phlegeton/epic/docs/images/pbalt.jpg

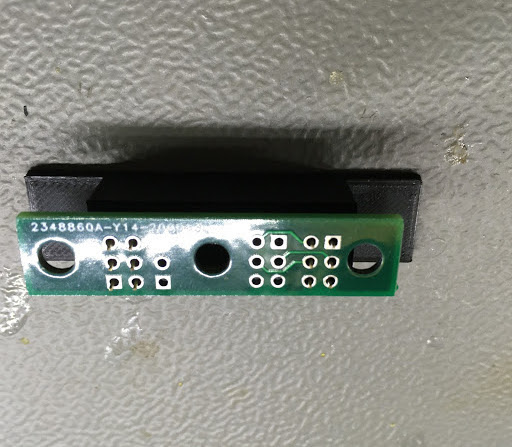
docs/images/pbalt.jpg
