phlegeton/epic/docs/images/pichatas.jpg

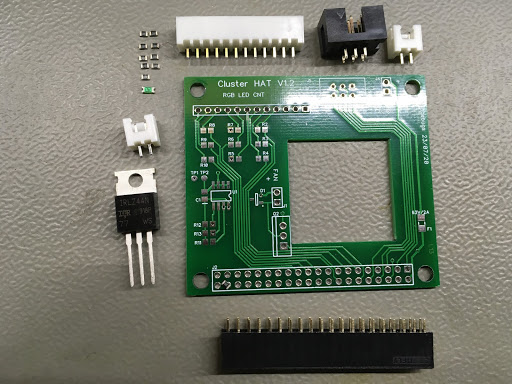
docs/images/pichatas.jpg
