phlegeton/epic/docs/images/pichfix.jpg

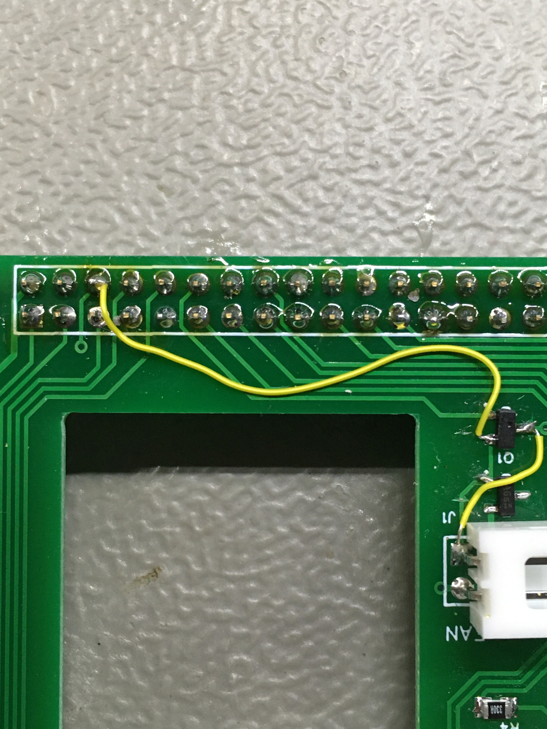
docs/images/pichfix.jpg
