phlegeton/epic/docs/images/pitp2.jpg

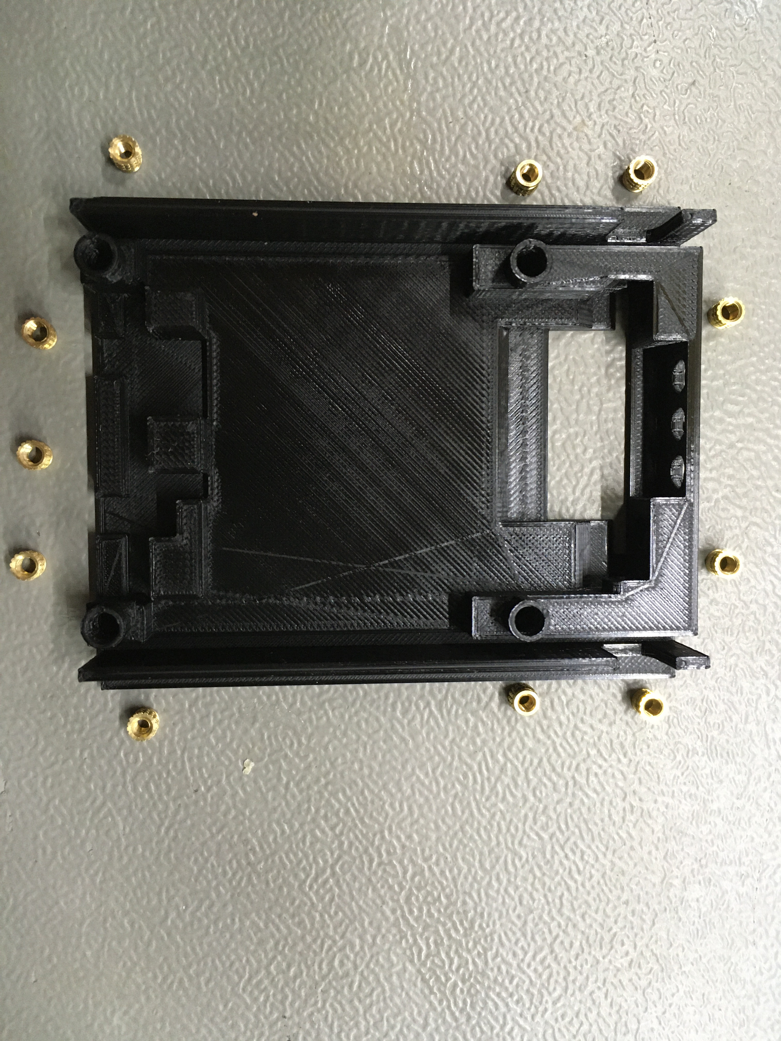
docs/images/pitp2.jpg
