phlegeton/epic/docs/images/rgb_cbl_orientation.jpg

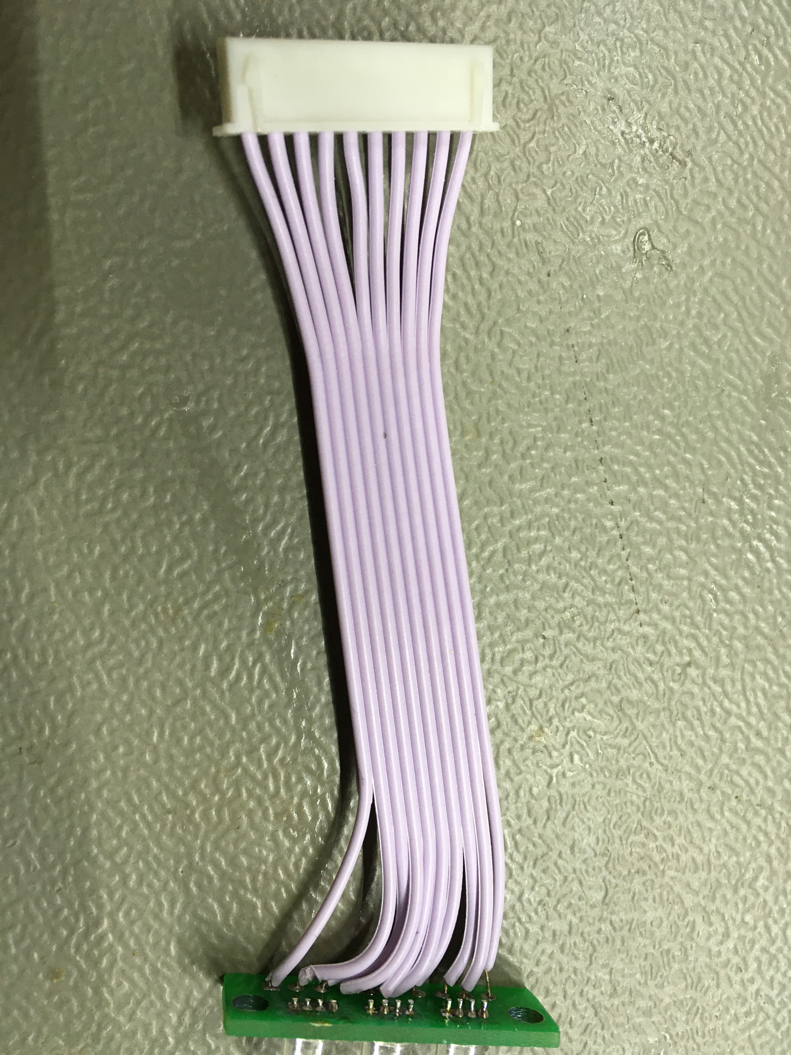
docs/images/rgb_cbl_orientation.jpg
