phlegeton/epic/docs/images/srgblwht.jpg

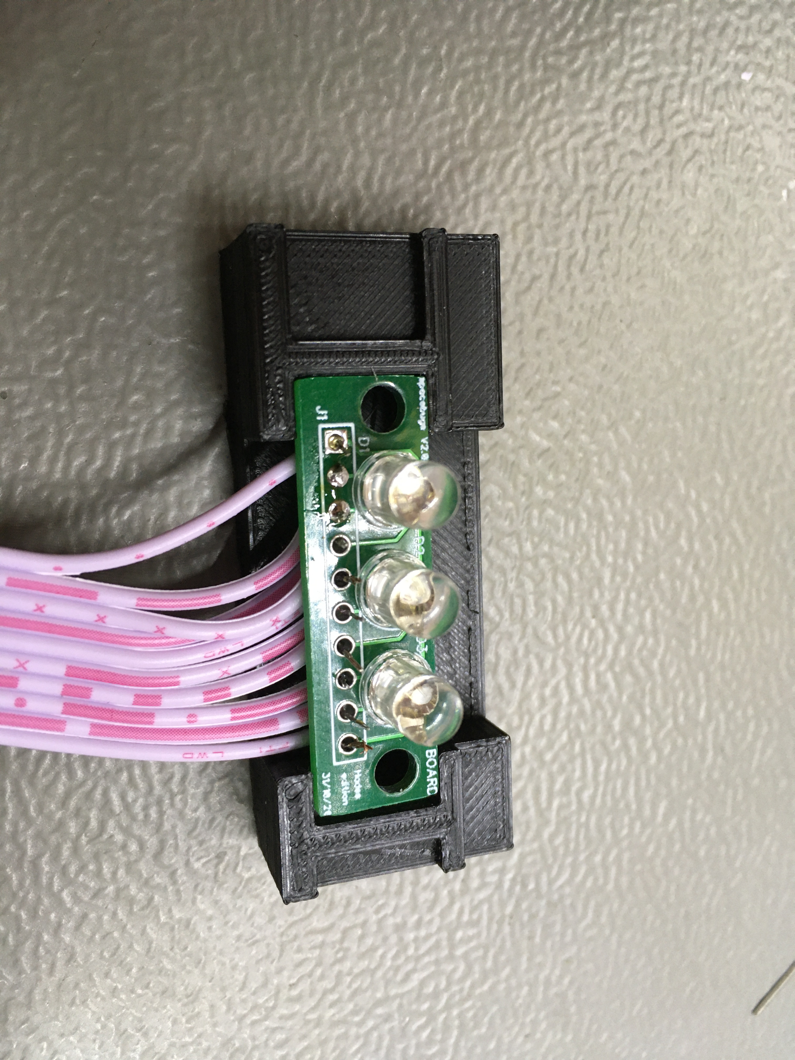
docs/images/srgblwht.jpg
